irkit/device/case/IRKit.jpg

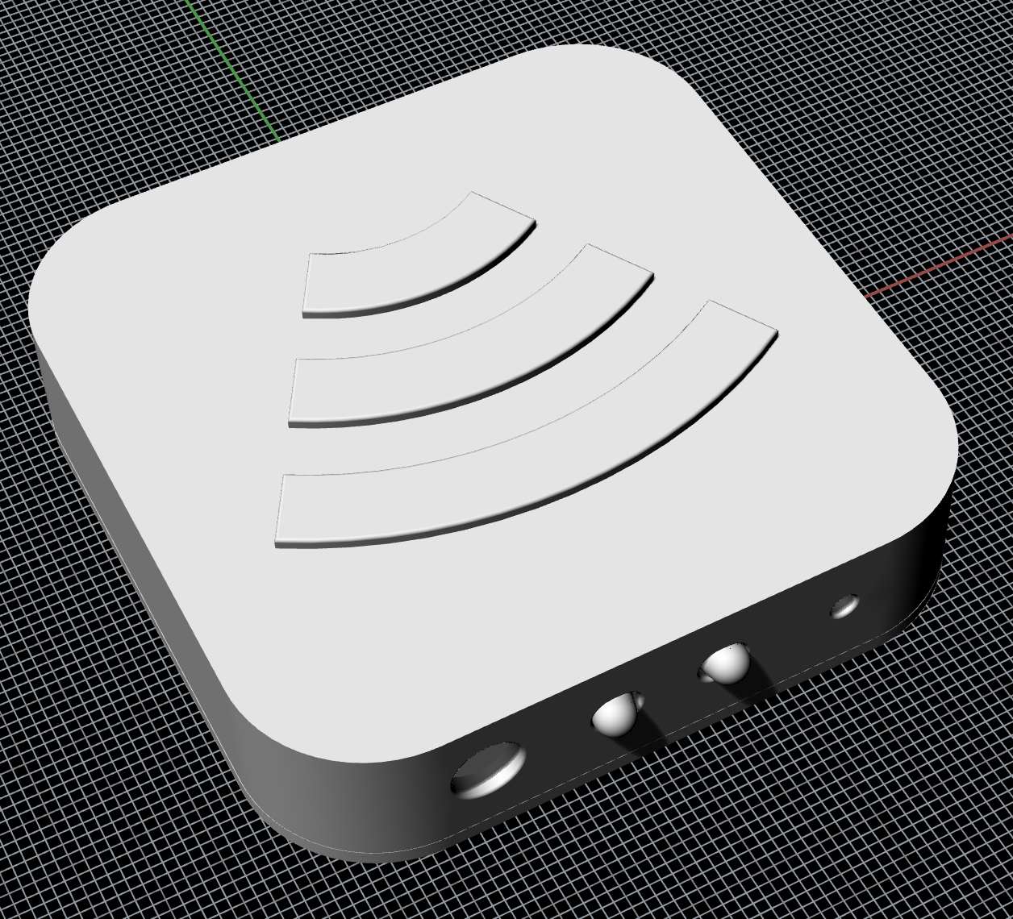
case/IRKit.jpg
