irkit/device/spec/diagrams/ir-send.png

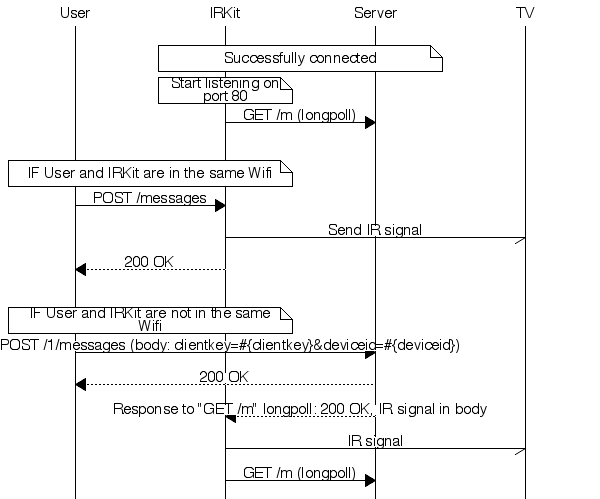
spec/diagrams/ir-send.png
