irkit/device/spec/diagrams/setup.png

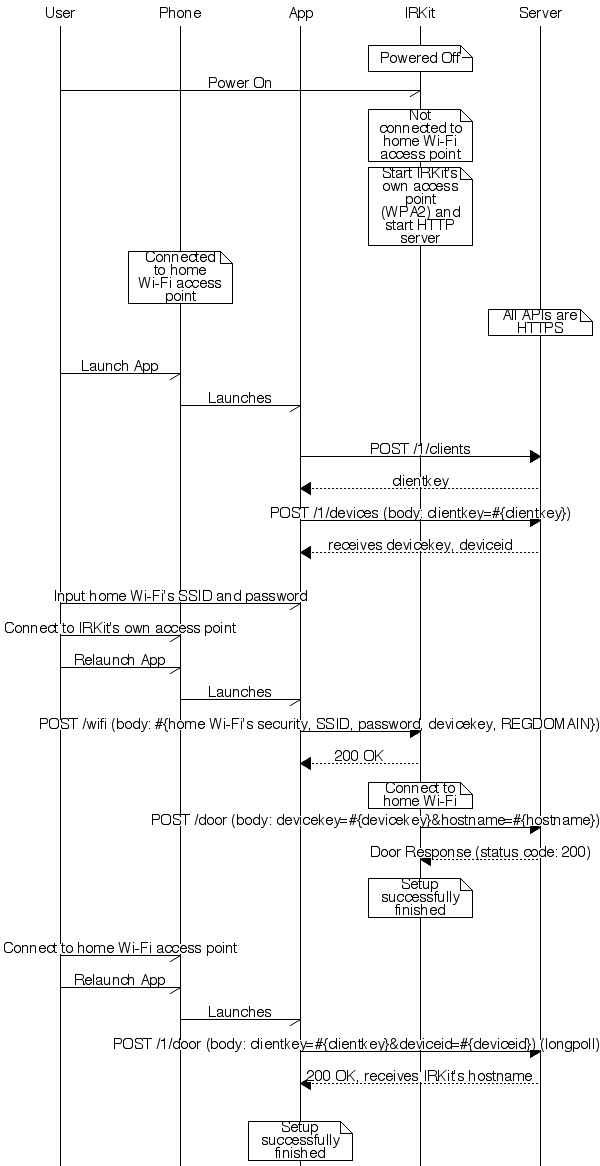
spec/diagrams/setup.png
