irkit/device/hardware/simulation/irled.asc

C1: cap; 4.7u
D1: diode; LD271
D2: diode; LD271
Q1: npn; 2SD1781K
R1: res; 1.8k
R2: res; 10
R3: res; 10k
R4: res; 10
V1: voltage; PULSE(0V 5V 18u 0 0 9u 27u 100); AC 2.5V
V2: voltage; 5V
Named nets: 0, in, b, e, c, out
.tran 0.1m
