irkit/device/hardware/simulation/microphone.ASC

C1: cap; 1u
C2: cap; 10u
C3: cap; 0.047u
R1: res; 2k
R2: res; 1.3k
R3: res; 2k
R4: res; 10
U1: LM386
V1: voltage; SINE(2.5 0.1 10k)
V2: voltage; 3.3
V3: voltage; 5
Named nets: 0
.tran 0 0.001 0
