irkit/device/firmware/src/IRKit/IRKitJSONParser.c

/*
 Copyright (C) 2013-2014 Masakazu Ohtsuka
  
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
 You should have received a copy of the GNU General Public License
 along with this program.  If not, see <http://www.gnu.org/licenses/>.
*/
#include "IRKitJSONParser.h"

void irkit_json_parse (char letter,
                       JSONParserStartEnd on_start,
                       JSONParserData on_data,
                       JSONParserStartEnd on_end) {
    static uint8_t  current_token;
    static uint32_t data;
    static uint8_t  data_exists;
    static uint8_t  first_letter_of_key;
    static uint8_t  is_key;
    static char     pass[10];
    static uint8_t  pass_index;
    static uint8_t  before_colon;

    // special case only json parser (don't try to reuse this)
    // non-nested Object with following possible keys
    // (check only the first 2 letters to identify key)
    // - ID
    // - FOrmat
    // - FReq
    // - DAta
    // - Pass
    switch (letter) {
    case '{':
        is_key = 0;
        before_colon = 1;
        on_start();
        break;
    case '}':
        if (data_exists) {
            on_data(current_token, data, pass);
        }
        on_end();
        break;
    case '"':
        if ( (! is_key) && before_colon ) {
            // detected JSON Object's key
            is_key              = 1;
            first_letter_of_key = 0;
            current_token       = IrJsonParserDataKeyUnknown;
        }
        else {
            is_key              = 0;
        }
        break;
    case ':':
        data          = 0;
        data_exists   = 0;
        pass_index    = 0;
        before_colon  = 0;
        break;
    case '0':
    case '1':
    case '2':
    case '3':
    case '4':
    case '5':
    case '6':
    case '7':
    case '8':
    case '9':
    case 'X':
        if ( (current_token == IrJsonParserDataKeyId)   ||
             (current_token == IrJsonParserDataKeyFreq) ||
             (current_token == IrJsonParserDataKeyData) ) {
            if (data_exists) {
                data    *= 10;
            }
            data        += (letter - '0');
            data_exists  = 1;
        }
        else if (current_token == IrJsonParserDataKeyPass) {
            if (pass_index > 9) {
                return;
            }
            pass[ pass_index ] = letter;
            pass_index ++;
            data_exists = 1;
        }
        break;
    case ',':
    case ']':
        if (data_exists) {
            on_data(current_token, data, pass);
            data        = 0;
            data_exists = 0;
        }
        before_colon = 1;
        break;
    default:
        break;
    }

    if (is_key && (letter != '"')) {
        if (! first_letter_of_key) {
            // save key's first letter
            first_letter_of_key = letter;
        }
        else if (current_token == IrJsonParserDataKeyUnknown) {
            // - id
            // - format
            // - freq
            // - data
            // - pass
            if (first_letter_of_key == 'i' && letter == 'd') {
                current_token = IrJsonParserDataKeyId;
            }
            else if (first_letter_of_key == 'f' && letter == 'o') {
                current_token = IrJsonParserDataKeyFormat;
            }
            else if (first_letter_of_key == 'f' && letter == 'r') {
                current_token = IrJsonParserDataKeyFreq;
            }
            else if (first_letter_of_key == 'd' && letter == 'a') {
                current_token = IrJsonParserDataKeyData;
            }
            else if (first_letter_of_key == 'p' && letter == 'a') {
                current_token = IrJsonParserDataKeyPass;
            }
        }
    }
}
